quattroerik/Vindriktning-plus/src/secret_template.h

//rename this file to secret.h
//update with your information

#define SECRET_SSID "your wifi SID"
#define SECRET_WIFI_PASSWORD "your wifi password"
#define SECRET_MQTT_SERVER "192.168.0.5"
#define SECRET_MQTT_PORT 1883
#define SECRET_MQTT_USER "mqtt user name"
#define SECRET_MQTT_PASSWORD "mqtt password"
#define SECRET_MQTT_CLIENT_ID "mqtt client id name"
#define SECRET_Name "not really a secret"
